AdmiralAki99/R.I.O/src/dig_hour_40px.c

/*******************************************************************************
 * Size: 40 px
 * Bpp: 1
 * Opts: 
 ******************************************************************************/

#ifdef LV_LVGL_H_INCLUDE_SIMPLE
#include "lvgl.h"
#else
#include "lvgl.h"
#endif

#ifndef DIG_HOUR_40PX
#define DIG_HOUR_40PX 1
#endif

#if DIG_HOUR_40PX

/*-----------------
 *    BITMAPS
 *----------------*/

/*Store the image of the glyphs*/
static LV_ATTRIBUTE_LARGE_CONST const uint8_t glyph_bitmap[] = {
    /* U+0030 "0" */
    0x3, 0xf8, 0x1, 0xff, 0xc0, 0x7f, 0xfc, 0x1f,
    0xff, 0xc7, 0xf1, 0xfc, 0xfc, 0x1f, 0x9f, 0x3,
    0xf7, 0xe0, 0x3f, 0xfc, 0x7, 0xff, 0x80, 0xff,
    0xf0, 0x1f, 0xfe, 0x3, 0xff, 0xc0, 0x7f, 0xf8,
    0xf, 0xff, 0x1, 0xff, 0xe0, 0x3f, 0xfc, 0x7,
    0xff, 0x80, 0xff, 0xf0, 0x1f, 0xfe, 0x3, 0xff,
    0xc0, 0x7f, 0xf8, 0xf, 0xdf, 0x83, 0xf3, 0xf0,
    0x7e, 0x7f, 0x1f, 0xc7, 0xff, 0xf0, 0x7f, 0xfc,
    0x7, 0xff, 0x0, 0x3f, 0x80,

    /* U+0031 "1" */
    0x0, 0x18, 0x7, 0xc1, 0xfe, 0x3f, 0xff, 0xff,
    0xff, 0xff, 0xff, 0xff, 0x3f, 0xc1, 0xf8, 0xf,
    0xc0, 0x7e, 0x3, 0xf0, 0x1f, 0x80, 0xfc, 0x7,
    0xe0, 0x3f, 0x1, 0xf8, 0xf, 0xc0, 0x7e, 0x3,
    0xf0, 0x1f, 0x80, 0xfc, 0x7, 0xe0, 0x3f, 0x1,
    0xf8, 0xf, 0xc0, 0x7e, 0x3, 0xf0, 0x1f, 0x80,

    /* U+0032 "2" */
    0x3, 0xfc, 0x0, 0xff, 0xf0, 0x1f, 0xff, 0x83,
    0xff, 0xfc, 0x7f, 0x1f, 0xc7, 0xe0, 0xfe, 0xfc,
    0x7, 0xef, 0xc0, 0x7e, 0xfc, 0x7, 0xe0, 0x0,
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
    0xc0, 0x0, 0x7e, 0x0, 0x3, 0xf8, 0x0, 0x1f,
    0xc0, 0x0, 0x7e, 0x0, 0x3, 0xf8, 0x0, 0xf,
    0xc0, 0x0, 0x7f, 0x0, 0x3, 0xff, 0xff, 0xff,
    0xff, 0xff, 0xff, 0xff, 0xff, 0xff, 0xff, 0xfc
};


/*---------------------
 *  GLYPH DESCRIPTION
 *--------------------*/

static const lv_font_fmt_txt_glyph_dsc_t glyph_dsc[] = {
    {.bitmap_index = 0, .adv_w = 0, .box_w = 0, .box_h = 0, .ofs_x = 0, .ofs_y = 0} /* id = 0 reserved */,
    {.bitmap_index = 0, .adv_w = 367, .box_w = 19, .box_h = 29, .ofs_x = 2, .ofs_y = 0},
    {.bitmap_index = 69, .adv_w = 367, .box_w = 13, .box_h = 29, .ofs_x = 3, .ofs_y = 0},
    {.bitmap_index = 117, .adv_w = 367, .box_w = 20, .box_h = 29, .ofs_x = 1, .ofs_y = 0},
    {.bitmap_index = 190, .adv_w = 367, .box_w = 20, .box_h = 29, .ofs_x = 1, .ofs_y = 0},
    {.bitmap_index = 263, .adv_w = 367, .box_w = 21, .box_h = 29, .ofs_x = 1, .ofs_y = 0},
    {.bitmap_index = 340, .adv_w = 367, .box_w = 20, .box_h = 29, .ofs_x = 2, .ofs_y = 0},
    {.bitmap_index = 413, .adv_w = 367, .box_w = 20, .box_h = 29, .ofs_x = 2, .ofs_y = 0},
    {.bitmap_index = 486, .adv_w = 367, .box_w = 20, .box_h = 29, .ofs_x = 1, .ofs_y = 0},
    {.bitmap_index = 559, .adv_w = 367, .box_w = 19, .box_h = 29, .ofs_x = 2, .ofs_y = 0},
    {.bitmap_index = 628, .adv_w = 367, .box_w = 19, .box_h = 29, .ofs_x = 2, .ofs_y = 0},
    {.bitmap_index = 697, .adv_w = 431, .box_w = 27, .box_h = 29, .ofs_x = 0, .ofs_y = 0},
    {.bitmap_index = 795, .adv_w = 408, .box_w = 21, .box_h = 29, .ofs_x = 3, .ofs_y = 0},
    {.bitmap_index = 872, .adv_w = 419, .box_w = 23, .box_h = 29, .ofs_x = 2, .ofs_y = 0},
    {.bitmap_index = 956, .adv_w = 416, .box_w = 22, .box_h = 29, .ofs_x = 3, .ofs_y = 0},
    {.bitmap_index = 1036, .adv_w = 360, .box_w = 19, .box_h = 29, .ofs_x = 3, .ofs_y = 0},
    {.bitmap_index = 1105, .adv_w = 351, .box_w = 19, .box_h = 29, .ofs_x = 3, .ofs_y = 0},
    {.bitmap_index = 1174, .adv_w = 436, .box_w = 23, .box_h = 29, .ofs_x = 2, .ofs_y = 0},
    {.bitmap_index = 1258, .adv_w = 452, .box_w = 23, .box_h = 29, .ofs_x = 3, .ofs_y = 0},
    {.bitmap_index = 1342, .adv_w = 187, .box_w = 6, .box_h = 29, .ofs_x = 3, .ofs_y = 0},
    {.bitmap_index = 1364, .adv_w = 358, .box_w = 19, .box_h = 29, .ofs_x = 1, .ofs_y = 0},
    {.bitmap_index = 1433, .adv_w = 406, .box_w = 23, .box_h = 29, .ofs_x = 3, .ofs_y = 0},
    {.bitmap_index = 1517, .adv_w = 347, .box_w = 19, .box_h = 29, .ofs_x = 3, .ofs_y = 0},
    {.bitmap_index = 1586, .adv_w = 561, .box_w = 30, .box_h = 29, .ofs_x = 3, .ofs_y = 0},
    {.bitmap_index = 1695, .adv_w = 452, .box_w = 23, .box_h = 29, .ofs_x = 3, .ofs_y = 0},
    {.bitmap_index = 1779, .adv_w = 442, .box_w = 24, .box_h = 29, .ofs_x = 2, .ofs_y = 0},
    {.bitmap_index = 1866, .adv_w = 413, .box_w = 22, .box_h = 29, .ofs_x = 3, .ofs_y = 0},
    {.bitmap_index = 1946, .adv_w = 442, .box_w = 24, .box_h = 34, .ofs_x = 2, .ofs_y = -5},
    {.bitmap_index = 2048, .adv_w = 408, .box_w = 22, .box_h = 29, .ofs_x = 3, .ofs_y = 0},
    {.bitmap_index = 2128, .adv_w = 393, .box_w = 22, .box_h = 29, .ofs_x = 1, .ofs_y = 0},
    {.bitmap_index = 2208, .adv_w = 396, .box_w = 23, .box_h = 29, .ofs_x = 1, .ofs_y = 0},
    {.bitmap_index = 2292, .adv_w = 421, .box_w = 22, .box_h = 29, .ofs_x = 2, .ofs_y = 0},
    {.bitmap_index = 2372, .adv_w = 418, .box_w = 26, .box_h = 29, .ofs_x = 0, .ofs_y = 0},
    {.bitmap_index = 2467, .adv_w = 560, .box_w = 33, .box_h = 29, .ofs_x = 1, .ofs_y = 0},
    {.bitmap_index = 2587, .adv_w = 407, .box_w = 25, .box_h = 29, .ofs_x = 0, .ofs_y = 0},
    {.bitmap_index = 2678, .adv_w = 396, .box_w = 24, .box_h = 29, .ofs_x = 0, .ofs_y = 0},
    {.bitmap_index = 2765, .adv_w = 388, .box_w = 22, .box_h = 29, .ofs_x = 1, .ofs_y = 0}
};

/*---------------------
 *  CHARACTER MAPPING
 *--------------------*/



/*Collect the unicode lists and glyph_id offsets*/
static const lv_font_fmt_txt_cmap_t cmaps[] =
{
    {
        .range_start = 48, .range_length = 10, .glyph_id_start = 1,
        .unicode_list = NULL, .glyph_id_ofs_list = NULL, .list_length = 0, .type = LV_FONT_FMT_TXT_CMAP_FORMAT0_TINY
    },
    {
        .range_start = 65, .range_length = 26, .glyph_id_start = 11,
        .unicode_list = NULL, .glyph_id_ofs_list = NULL, .list_length = 0, .type = LV_FONT_FMT_TXT_CMAP_FORMAT0_TINY
    }
};

/*-----------------
 *    KERNING
 *----------------*/


/*Map glyph_ids to kern left classes*/
static const uint8_t kern_left_class_mapping[] =
{
    0, 0, 0, 0, 0, 0, 0, 0,
    0, 0, 0, 1, 2, 3, 4, 5,
    6, 0, 7, 7, 8, 9, 10, 7,
    7, 4, 11, 12, 13, 0, 14, 8,
    15, 16, 17, 18, 19
};

/*Map glyph_ids to kern right classes*/
static const uint8_t kern_right_class_mapping[] =
{
    0, 0, 0, 0, 0, 0, 0, 0,
    0, 0, 0, 1, 0, 2, 0, 0,
    0, 2, 0, 0, 3, 0, 0, 0,
    0, 2, 0, 2, 0, 4, 5, 6,
    7, 8, 9, 10, 11
};

/*Kern values between classes*/
static const int8_t kern_class_values[] =
{
    0, -7, 0, 0, -37, -5, -24, -12,
    0, -47, 0, 0, 0, 0, 0, -8,
    0, -7, 0, 0, -17, 0, 0, 0,
    0, 0, -9, 0, 0, 0, 0, 0,
    0, -7, 0, 0, 0, -27, 0, -7,
    0, -7, -13, -7, 0, 0, 0, 0,
    6, 0, 0, 0, 0, 0, 0, -60,
    0, -65, 0, 6, 0, 0, 0, 0,
    0, 0, 6, 0, 0, 0, -9, 0,
    0, 0, 5, -9, 0, -7, 0, 0,
    0, 0, 0, 0, 0, 0, 0, 0,
    0, -10, 0, 0, 0, 0, 0, 0,
    0, 0, 0, 6, -20, 0, 0, -64,
    -7, -64, -29, 0, -87, 0, -56, 0,
    -57, 0, 0, 0, 0, 0, -16, 0,
    -11, 0, 0, 0, 0, -10, 0, -9,
    -6, 0, -11, 0, 0, 0, 0, 0,
    -16, 0, -6, 0, 0, -15, 0, -37,
    -9, -67, -5, 5, 0, 5, 5, 0,
    5, 0, -23, -4, 0, 0, 0, 0,
    0, 0, 0, 0, 0, -13, 0, 0,
    0, 4, 0, 0, 0, 0, 0, 0,
    0, -8, 0, 0, 0, 0, 4, 0,
    0, 0, 0, -47, -9, -30, -5, 5,
    -30, 6, 5, 4, 6, 0, 4, -8,
    0, 0, 0, 0, 0, 0, 0, 0,
    0
};


/*Collect the kern class' data in one place*/
static const lv_font_fmt_txt_kern_classes_t kern_classes =
{
    .class_pair_values   = kern_class_values,
    .left_class_mapping  = kern_left_class_mapping,
    .right_class_mapping = kern_right_class_mapping,
    .left_class_cnt      = 19,
    .right_class_cnt     = 11,
};

/*--------------------
 *  ALL CUSTOM DATA
 *--------------------*/

#if LV_VERSION_CHECK(8, 0, 0)
/*Store all the custom data of the font*/
static  lv_font_fmt_txt_glyph_cache_t cache;
static const lv_font_fmt_txt_dsc_t font_dsc = {
#else
static lv_font_fmt_txt_dsc_t font_dsc = {
#endif
    .glyph_bitmap = glyph_bitmap,
    .glyph_dsc = glyph_dsc,
    .cmaps = cmaps,
    .kern_dsc = &kern_classes,
    .kern_scale = 16,
    .cmap_num = 2,
    .bpp = 1,
    .kern_classes = 1,
    .bitmap_format = 0,
#if LV_VERSION_CHECK(8, 0, 0)
    .cache = &cache
#endif
};


/*-----------------
 *  PUBLIC FONT
 *----------------*/

/*Initialize a public general font descriptor*/
#if LV_VERSION_CHECK(8, 0, 0)
const lv_font_t dig_hour_40px = {
#else
lv_font_t dig_hour_40px = {
#endif
    .get_glyph_dsc = lv_font_get_glyph_dsc_fmt_txt,    /*Function pointer to get glyph's data*/
    .get_glyph_bitmap = lv_font_get_bitmap_fmt_txt,    /*Function pointer to get glyph's bitmap*/
    .line_height = 34,          /*The maximum line height required by the font*/
    .base_line = 5,             /*Baseline measured from the bottom of the line*/
#if !(LVGL_VERSION_MAJOR == 6 && LVGL_VERSION_MINOR == 0)
    .subpx = LV_FONT_SUBPX_NONE,
#endif
#if LV_VERSION_CHECK(7, 4, 0) || LVGL_VERSION_MAJOR >= 8
    .underline_position = -3,
    .underline_thickness = 2,
#endif
    .dsc = &font_dsc           /*The custom font data. Will be accessed by `get_glyph_bitmap/dsc` */
};



#endif /*#if DIG_HOUR_40PX*/
