AdmiralAki99/R.I.O/src/thumb_test.h

//
// thumb_test
//
const uint8_t thumb_test[] PROGMEM = {	0xff,0xd8,0xff,0xe1,0x1e,0x28,0x45,0x78,0x69,0x66,0x00,0x00,0x4d,0x4d,0x00,0x2a,
	0x00,0x00,0x00,0x08,0x00,0x0d,0x01,0x00,0x00,0x03,0x00,0x00,0x00,0x01,0x0f,0xc0,
	0x00,0x00,0x01,0x01,0x00,0x03,0x00,0x00,0x00,0x01,0x0b,0xd0,0x00,0x00,0x01,0x0f,
	0x00,0x02,0x00,0x00,0x00,0x08,0x00,0x00,0x00,0xaa,0x01,0x10,0x00,0x02,0x00,0x00,
	0x00,0x0a,0x00,0x00,0x00,0xb2,0x01,0x12,0x00,0x03,0x00,0x00,0x00,0x01,0x00,0x06,
	0x00,0x00,0x01,0x1a,0x00,0x05,0x00,0x00,0x00,0x01,0x00,0x00,0x00,0xbc,0x01,0x1b,
	0x00,0x05,0x00,0x00,0x00,0x01,0x00,0x00,0x00,0xc4,0x01,0x28,0x00,0x03,0x00,0x00,
	0x00,0x01,0x00,0x02,0x00,0x00,0x01,0x31,0x00,0x02,0x00,0x00,0x00,0x0f,0x00,0x00,
	0x00,0xcc,0x01,0x32,0x00,0x02,0x00,0x00,0x00,0x14,0x00,0x00,0x00,0xdc,0x02,0x13,
	0x00,0x03,0x00,0x00,0x00,0x01,0x00,0x01,0x00,0x00,0x87,0x69,0x00,0x04,0x00,0x00,
	0x00,0x01,0x00,0x00,0x00,0xf0,0x88,0x25,0x00,0x04,0x00,0x00,0x00,0x01,0x00,0x00,
	0x03,0x20,0x00,0x00,0x03,0x26,0x73,0x61,0x6d,0x73,0x75,0x6e,0x67,0x00,0x53,0x4d,
	0x2d,0x47,0x39,0x36,0x35,0x55,0x31,0x00,0x00,0x00,0x00,0x48,0x00,0x00,0x00,0x01,
	0x00,0x00,0x00,0x48,0x00,0x00,0x00,0x01,0x47,0x39,0x36,0x35,0x55,0x31,0x55,0x45,
	0x53,0x37,0x44,0x54,0x45,0x31,0x00,0x00,0x32,0x30,0x32,0x30,0x3a,0x30,0x38,0x3a,
	0x30,0x39,0x20,0x31,0x34,0x3a,0x34,0x32,0x3a,0x31,0x33,0x00,0x00,0x1f,0x82,0x9a,
	0x00,0x05,0x00,0x00,0x00,0x01,0x00,0x00,0x02,0x6a,0x82,0x9d,0x00,0x05,0x00,0x00,
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
	0x00, 0x00, 0x00, 0x00, 0x00, 0x00, 0x00, 0x00, 0x00, 0x00, 0x00, 0x00, 0x00, 0x00, 0x00, 0x1f, 
	0xff, 0xff, 0xff, 0xff, 0xff, 0xff, 0x00, 0x00, 0x00, 0x00, 0x00, 0x00, 0x00, 0x00, 0x00, 0x00, 
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
};
